eblair363/4-Stage-BJT-Amplifier/sim/pspice/bwGainNoCursor.png

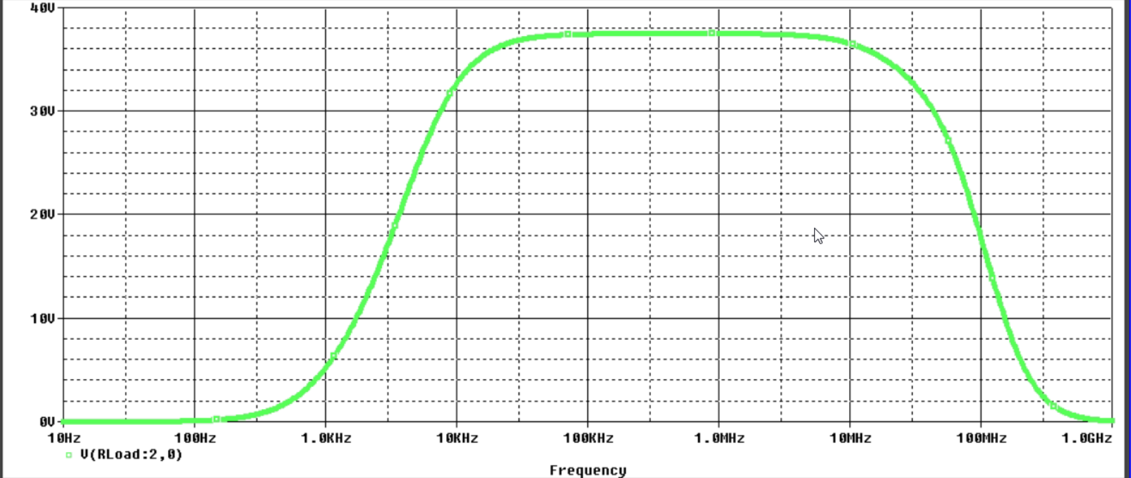
sim/pspice/bwGainNoCursor.png
