eblair363/4-Stage-BJT-Amplifier/sim/pspice/inputimpedanceNoCursor.png

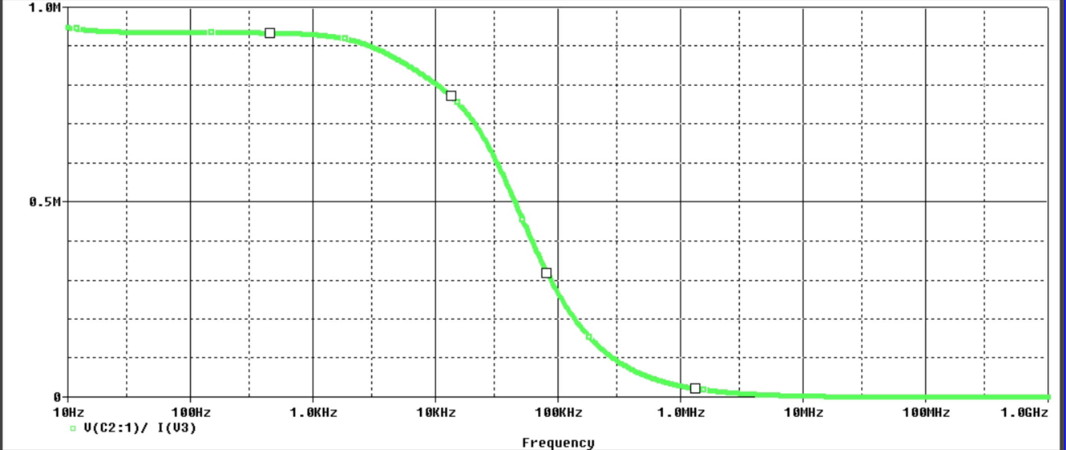
sim/pspice/inputimpedanceNoCursor.png
