eblair363/4-Stage-BJT-Amplifier/sim/pspice/outputpower.png

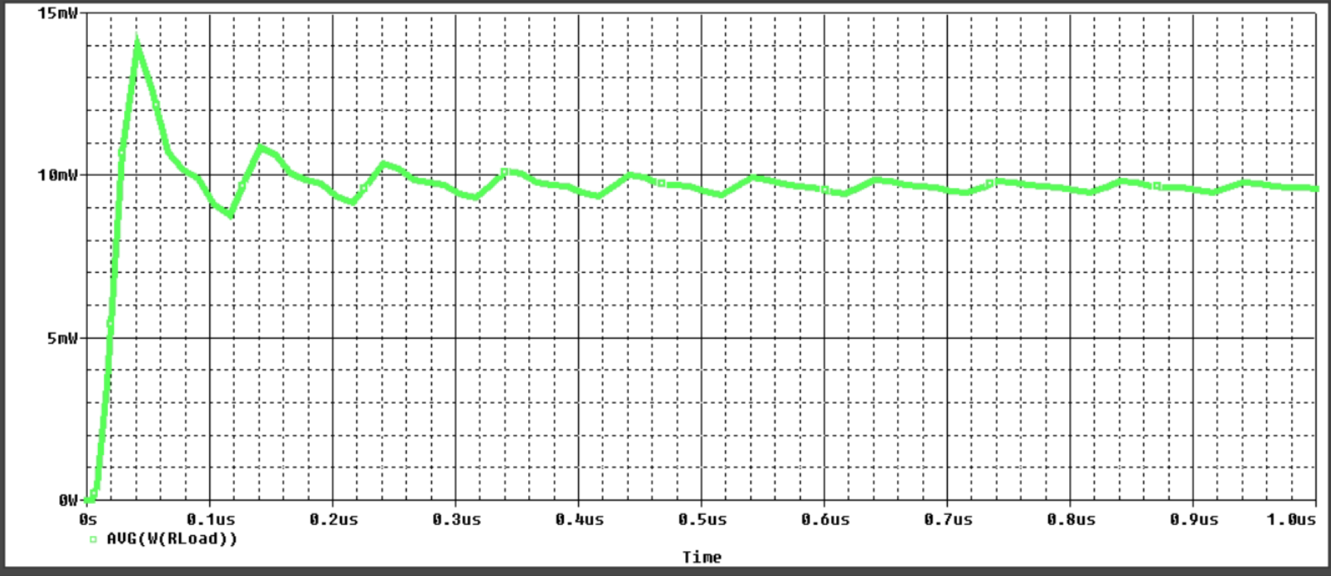
sim/pspice/outputpower.png
