eblair363/4-Stage-BJT-Amplifier/sim/pspice/schematicRe2_2k.png

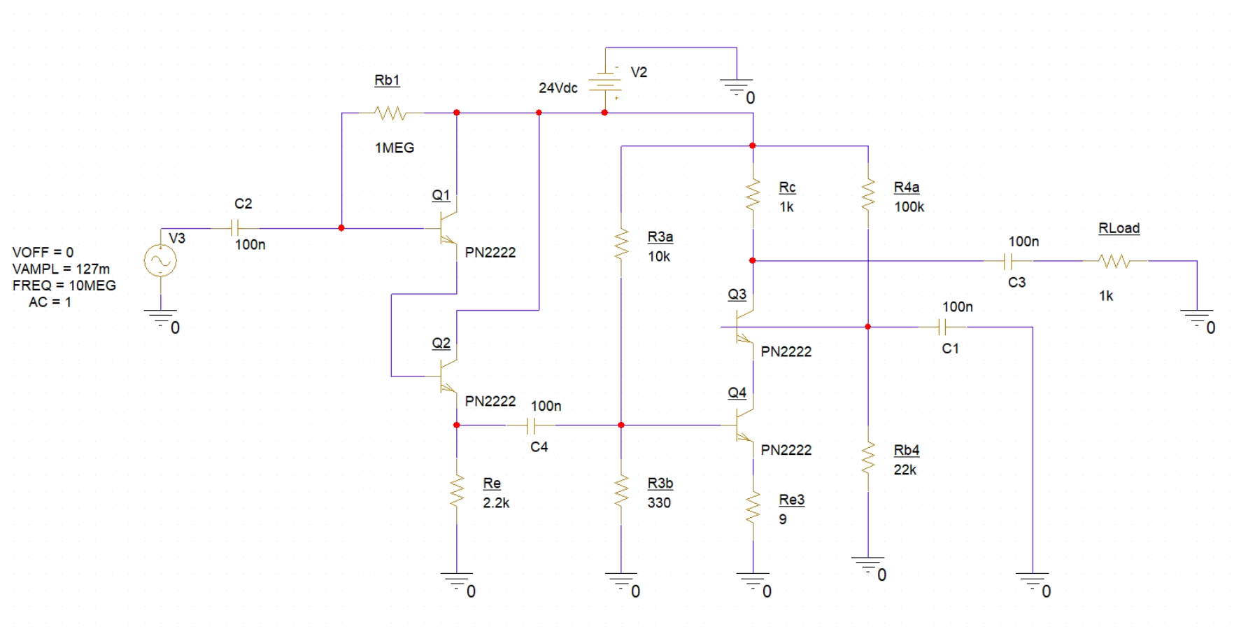
sim/pspice/schematicRe2_2k.png
