eblair363/4-Stage-BJT-Amplifier/sim/pspice/Vpeak_to_peak.png

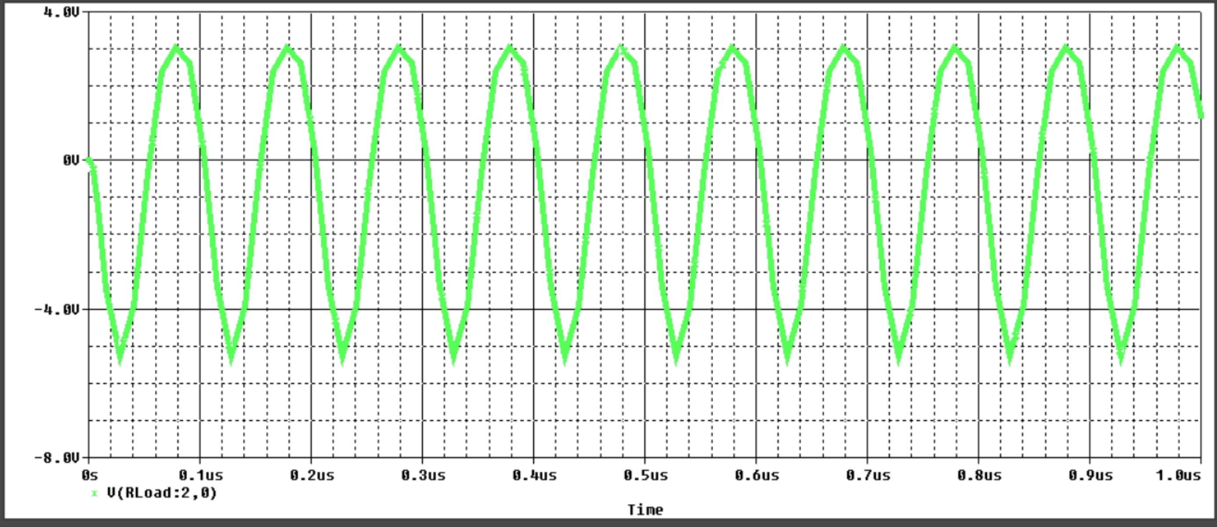
sim/pspice/Vpeak_to_peak.png
